BoujeeEnjinia1701/breakhook/cad/drawings/BHK-DWG-001.pdf

PRELIMINARY, NOT FOR FABRICATION | BreakHook · github.com/BoujeeEnjinia1701/breakhook

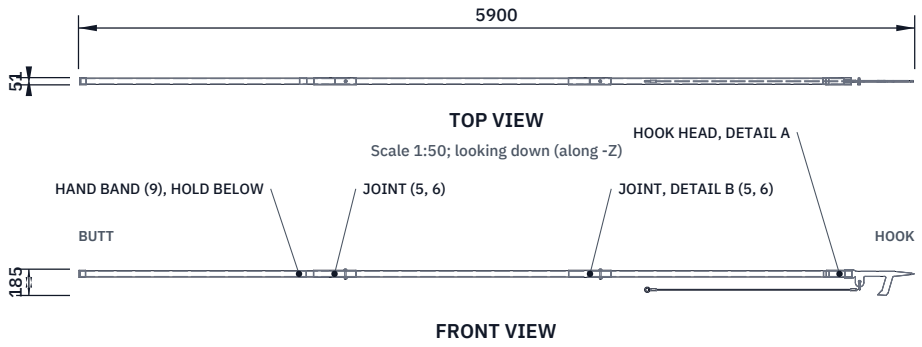
[picture p40: figure]
FRONT VIEW; TOP VIEW; Scale 1:50; looking down (along -Z); HAND BAND (9), HOLD BELOW; JOINT (5, 6); JOINT, DETAIL B (5, 6); HOOK HEAD, DETAIL A; BUTT; HOOK

Scale 1:50; looking at the front (along +Y)

RIGHT VIEW
Scale 1:50; looking at the right side (along -X)
1800 + CAP | 1800 | 1800 | HEAD

5900 OVERALL

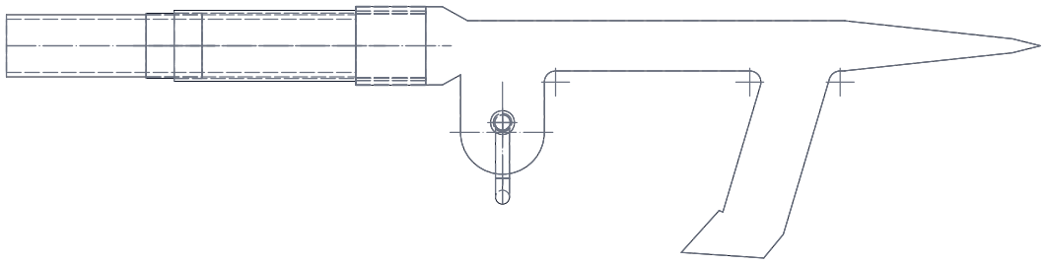
[picture p41: figure]

DETAIL A: HOOK HEAD
Scale 1:5; looking at the front (along +Y); pole tip shown cut short

DETAIL B: POLE JOINT
Scale 1:5; looking at the front (along +Y); sleeve bonded to the lower section

DETAIL C: FORK PROP (BOM 26 TO 31)
Scale 1:10; closed to 1.24 m, foot left, fork right; carried separately, sets the pole at mid-length

MAIN DIMENSIONS AND INTERFACES (MM)
Overall 5900; three sections 1800, 44.5 x 3.2 fibreglass, foam filled Joints: sleeve 50.8 x 3.2 x 300, bonded 150; nylon pin 10, 75 above joint Socket 50.8 x 2.0 x 180; pole goes in 130, 1.15 radial clearance
Plate 10 S355 in two 10.5 x 50 slots; four 6 fillet welds outside
Arm reaches 117 below the shank; throat 150 at the shank
Shackle hole 13, in line with the arm; 3/8 in bow shackle, WLL 1 t Leader 6 wire rope, 1500 eye to eye; pull rope 12 polyester, 25 m
Hand band 1550 from the butt; insulated length 3674
Pole and hook head 7.8 kg; working pull 3 kN, proof 6 kN
Fork prop 1.1 kg, notch 1.19 to 1.94 m; under the pole 2944 from the butt Third angle; pole along X, hook at +X; (n) = BOM line
REV | DESCRIPTION | DATE | BY
P1 | Preliminary GA of the constructable design (TRL 3; BHK-DDR-002) | 2026-10-03 | AC
P2 | Fork prop added, detail C (BHK-DDR-003) | 2026-10-03 | AC
BREAKHOOK | github.com/BoujeeEnjinia1701/breakhook

## Firebreak hook and pole set: general arrangement

DRAWING NO.
BHK-DWG-001

REV
P2

SHEET
1 of 1

SIZE

## ANSI B

SCALE
1:50

UNITS
mm
PROJECTION | DATE
2026-10-03

DRAWN
Amish Chadha

MATERIAL / NOTES
Hook head S355 plate in 50.8 x 2.0 steel tube, primed and painted; pole foam-filled fibreglass tube 44.5 x 3.2; see bom/bom.csv
Licensed CERN-OHL-S-2.0 · Design Molecule Lab · designmolecule.com | Generated from cad/src; do not edit by hand
