BoujeeEnjinia1701/breakhook/cad/drawings/BHK-DWG-101.pdf

### BUILD PLAN SKETCH, PLAN NOT YET BUILT BreakHook · github.com/BoujeeEnjinia1701/breakhook

FRONT VIEW
Scale 1:5; looking at the front (along +Y)

TOP VIEW
Scale 1:5; looking down (along -Z)

RIGHT VIEW
Scale 1:5; looking at the right side (along -X)

490

10 180

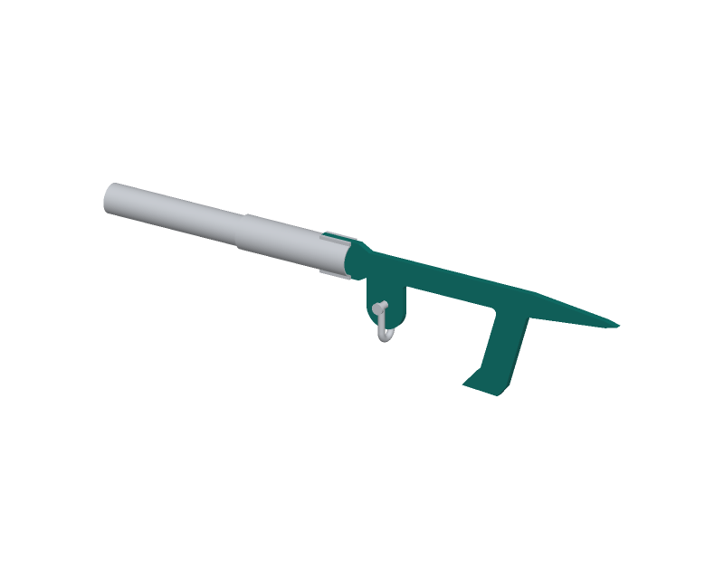
[picture p42: figure]

WHERE IT GOES
This part in colour, its neighbours in grey

HOW TO MAKE IT AND HOW IT FITS
Cut from 10 mm S355 plate, blank 500 x 200; one piece, no forging
Spike: tip on the centre line, 440 from the socket end of the plate
Shank 36 wide; the 56 wide end (62 long) goes into the socket slots
Arm 48 wide hangs 117 below the shank, raked back 17 deg; barb at its foot Rope tab under the shank, 25 to 85 from the socket end, round end R30 Shackle hole 13, centred 55 from the socket end and 55 below the axis Inside corners at the arm and tab: drill 16 and file to R8; no sharp notch Cut by plasma or chain drill and grinder; dress all edges, break corners 1 Throat between tab and arm: 150 wide at the shank, 128 at 100 below Fits: plate stands 2.6 proud of the tube top and bottom for the welds Check: lay on the full-size print; every edge within 1 mm
Stamp WLL 3 kN and the serial number on the shank before painting
REV | DESCRIPTION | DATE | BY
P1 | Making sketch for the prototype build plan | 2026-10-03 | AC
BREAKHOOK | github.com/BoujeeEnjinia1701/breakhook

## Hook plate: making sketch

DRAWING NO.
BHK-DWG-101

REV
P1

SHEET
1 of 1

SIZE

## ANSI B

SCALE
1:5

UNITS
mm
PROJECTION | DATE
2026-10-03

DRAWN
Amish Chadha

MATERIAL / NOTES
10 mm S355 steel plate, one per set
Licensed CERN-OHL-S-2.0 · Design Molecule Lab · designmolecule.com | Generated from cad/src; do not edit by hand
