BoujeeEnjinia1701/breakhook/cad/drawings/BHK-DWG-102.pdf

### BUILD PLAN SKETCH, PLAN NOT YET BUILT BreakHook · github.com/BoujeeEnjinia1701/breakhook

FRONT VIEW
Scale 1:2; looking at the front (along +Y)

TOP VIEW
Scale 1:2; looking down (along -Z)

RIGHT VIEW
Scale 1:2; looking at the right side (along -X)

180

51 51

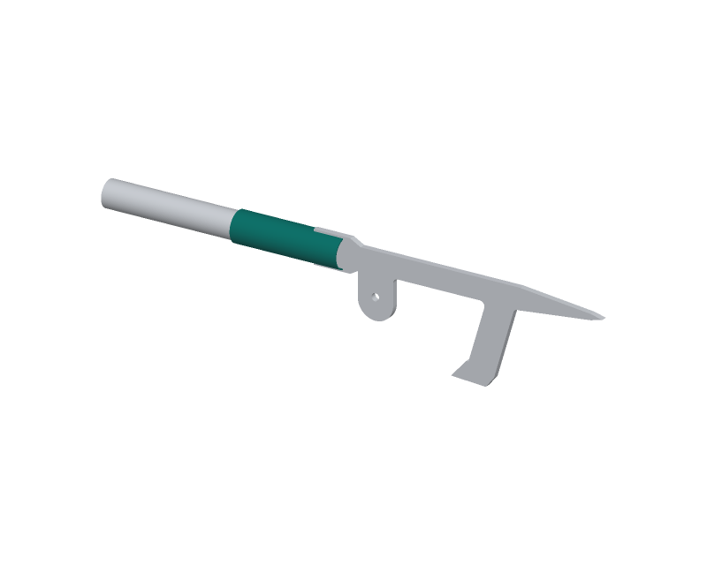
[picture p43: figure]

WHERE IT GOES
This part in colour, its neighbours in grey

HOW TO MAKE IT AND HOW IT FITS
Cut 180 long from 50.8 x 2.0 welded steel tube; square the ends
Slot one end across a diameter: two slots 10.5 wide, 50 deep, top and bottom Mark the slots with a strip of paper round the tube so they line up
Cut with a hacksaw or thin cutting disc; file to 10.5, square at the root
Deburr the bore at the open end and break its edge 1 x 45 deg
The bore is 46.8: the 44.5 pole slides in with 1.15 clearance each side The pole goes in 130 and stops against the end of the plate
Fits: the plate slides into both slots with no more than 0.5 total play Check: a 300 offcut of pole tube slides in and out by hand
REV | DESCRIPTION | DATE | BY
P1 | Making sketch for the prototype build plan | 2026-10-03 | AC
BREAKHOOK | github.com/BoujeeEnjinia1701/breakhook

## Socket tube: making sketch

DRAWING NO.
BHK-DWG-102

REV
P1

SHEET
1 of 1

SIZE

## ANSI B

SCALE
1:2

UNITS
mm
PROJECTION | DATE
2026-10-03

DRAWN
Amish Chadha

MATERIAL / NOTES
Welded steel tube 50.8 x 2.0, one per set
Licensed CERN-OHL-S-2.0 · Design Molecule Lab · designmolecule.com | Generated from cad/src; do not edit by hand
