BoujeeEnjinia1701/breakhook/cad/drawings/BHK-DWG-103.pdf

### BUILD PLAN SKETCH, PLAN NOT YET BUILT BreakHook · github.com/BoujeeEnjinia1701/breakhook

FRONT VIEW
Scale 1:10; looking at the front (along +Y)

TOP VIEW
Scale 1:10; looking down (along -Z)

RIGHT VIEW
Scale 1:10; looking at the right side (along -X)

1800

44 44

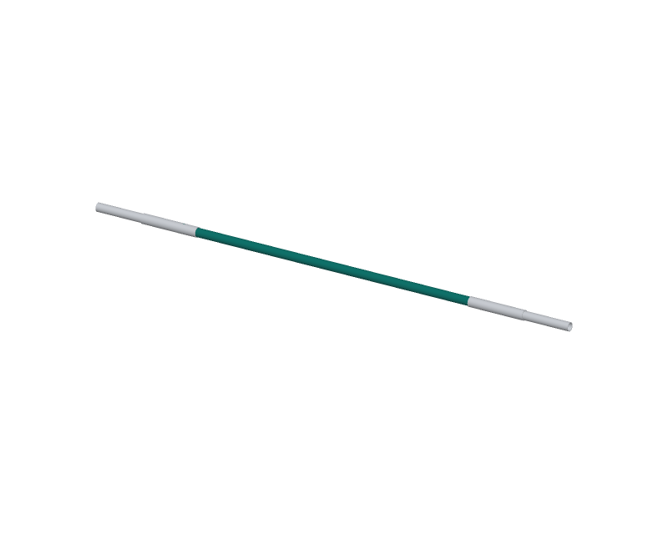
[picture p44: figure]

WHERE IT GOES
This part in colour, its neighbours in grey

HOW TO MAKE IT AND HOW IT FITS
Cut three lengths of 1800 from foam-filled fibreglass tube 44.5 x 3.2 Fine-tooth saw with the tube wrapped in tape; wear a dust mask outdoors Seal every cut end with a thin coat of epoxy so water cannot get into the foam Middle and top sections: drill one 10.5 hole across the tube, 74 from the bottom end (75 above the joint line), square to the tube, through both walls Butt section: no pin hole; its sleeve is bonded at its top end
Middle section: sleeve bonded at its top end; pin hole at its bottom end Top section: pin hole at its bottom end; friction ring at its top end
Coat each pin hole bore with epoxy as well
Check: each section 1800 within 2; holes square to the tube by eye
REV | DESCRIPTION | DATE | BY
P1 | Making sketch for the prototype build plan | 2026-10-03 | AC
BREAKHOOK | github.com/BoujeeEnjinia1701/breakhook

## Pole section (make 3): making sketch

DRAWING NO.
BHK-DWG-103

REV
P1

SHEET
1 of 1

SIZE

## ANSI B

SCALE
1:10

UNITS
mm
PROJECTION | DATE
2026-10-03

DRAWN
Amish Chadha

MATERIAL / NOTES
Foam-filled fibreglass tube 44.5 x 3.2, electrical grade
Licensed CERN-OHL-S-2.0 · Design Molecule Lab · designmolecule.com | Generated from cad/src; do not edit by hand
