BoujeeEnjinia1701/breakhook/cad/drawings/BHK-DWG-104.pdf

### BUILD PLAN SKETCH, PLAN NOT YET BUILT BreakHook · github.com/BoujeeEnjinia1701/breakhook

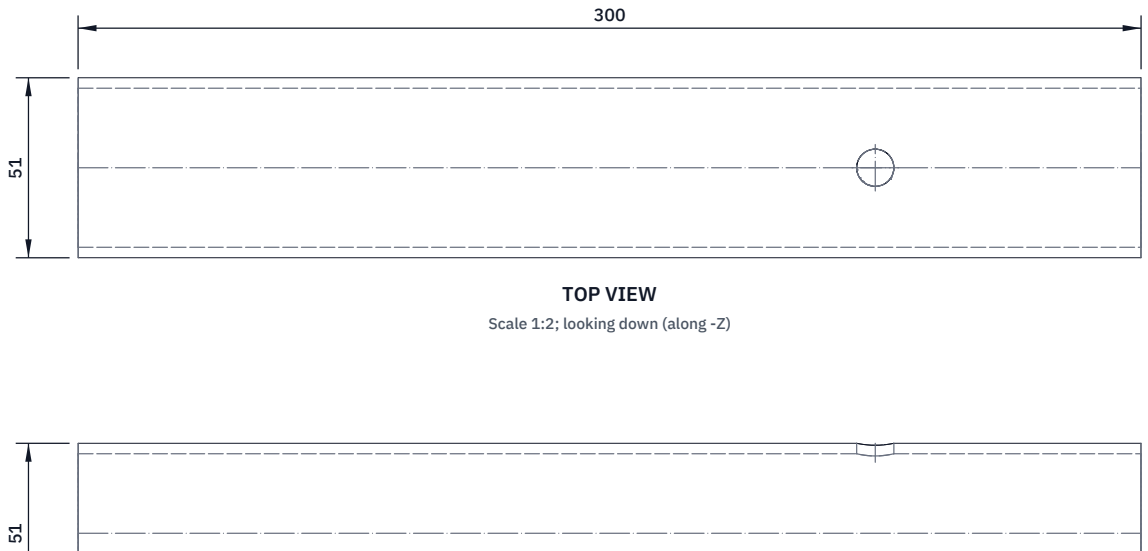
[picture p45: figure]
TOP VIEW; Scale 1:2; looking down (along -Z)

FRONT VIEW
Scale 1:2; looking at the front (along +Y)

RIGHT VIEW
Scale 1:2; looking at the right side (along -X)

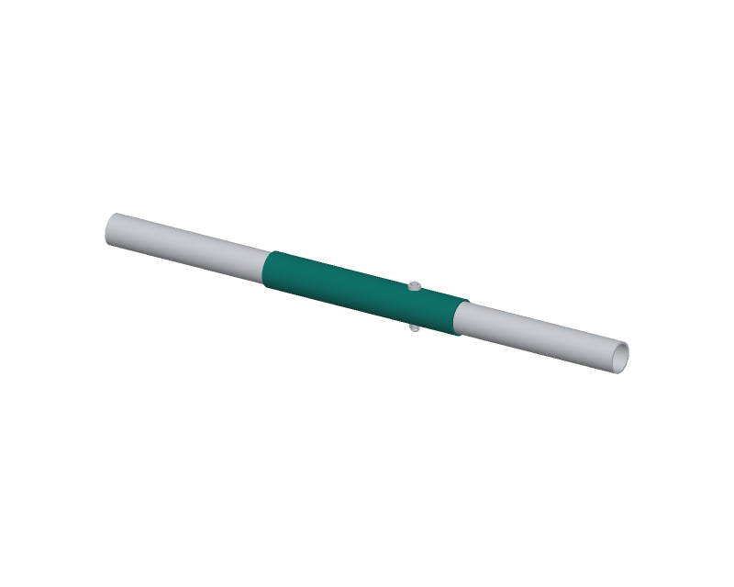
[picture p46: figure]

WHERE IT GOES
This part in colour, its neighbours in grey

HOW TO MAKE IT AND HOW IT FITS
Cut two lengths of 300 from 50.8 x 3.2 fibreglass tube; seal the ends
Sand the bore with coarse paper on a dowel until the pole tube slides in (about 0.2 clearance each side); try it often, do not overdo it
Drill one 10.5 hole across the sleeve, 75 from the middle (225 from one end) Bond the other half (150) onto the top of the lower section with epoxy,
the hole end sticking up; wipe off squeeze-out; cure a full day
Then slide the upper section in, drill through its pin hole into line
Check: upper section slides in and out by hand; the pin goes through both
REV | DESCRIPTION | DATE | BY
P1 | Making sketch for the prototype build plan | 2026-10-03 | AC
BREAKHOOK | github.com/BoujeeEnjinia1701/breakhook

## Joint sleeve (make 2): making sketch

DRAWING NO.
BHK-DWG-104

REV
P1

SHEET
1 of 1

SIZE

## ANSI B

SCALE
1:2

UNITS
mm
PROJECTION | DATE
2026-10-03

DRAWN
Amish Chadha

MATERIAL / NOTES
Fibreglass tube 50.8 x 3.2, 300 long
Licensed CERN-OHL-S-2.0 · Design Molecule Lab · designmolecule.com | Generated from cad/src; do not edit by hand
