BoujeeEnjinia1701/breakhook/cad/drawings/BHK-DWG-105.pdf

### BUILD PLAN SKETCH, PLAN NOT YET BUILT BreakHook · github.com/BoujeeEnjinia1701/breakhook

FRONT VIEW
Scale 1:5; looking at the front (along +Y)

TOP VIEW
Scale 1:5; looking down (along -Z)

RIGHT VIEW
Scale 1:5; looking at the right side (along -X)

32

300 32

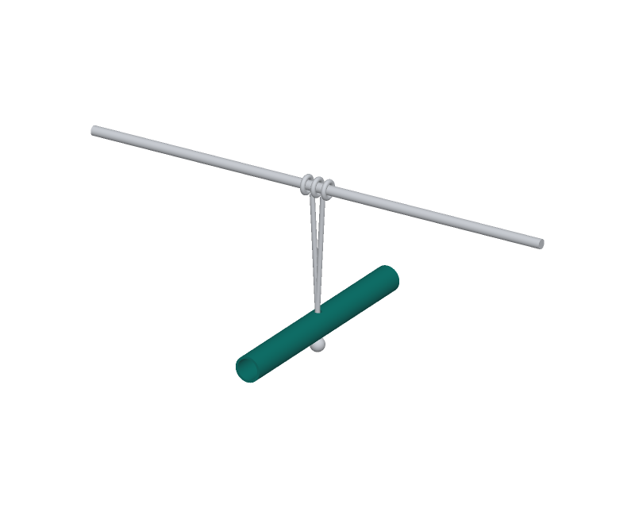
[picture p47: figure]

WHERE IT GOES
This part in colour, its neighbours in grey

HOW TO MAKE IT AND HOW IT FITS
Cut ten lengths of 300 from 32 x 3 fibreglass tube; round and seal the ends Drill a 10 hole straight across at mid length (150 from each end)
Sling: 1.2 m of 6 mm cord through the hole, tied into a loop with a
double fisherman's knot that sits under the toggle
Hitch the loop to the pull rope with a three-turn prusik hitch
(it slides when loose and grips when pulled)
Space the toggles 1 m apart, the first 11 m from the hook head Check: hang 30 kg on one toggle; the prusik must not slip
REV | DESCRIPTION | DATE | BY
P1 | Making sketch for the prototype build plan | 2026-10-03 | AC
BREAKHOOK | github.com/BoujeeEnjinia1701/breakhook

## Hauling toggle (make 10 per set): making sketch

DRAWING NO.
BHK-DWG-105

REV
P1

SHEET
1 of 1

SIZE

## ANSI B

SCALE
1:5

UNITS
mm
PROJECTION | DATE
2026-10-03

DRAWN
Amish Chadha

MATERIAL / NOTES
Fibreglass tube 32 x 3, 300 long
Licensed CERN-OHL-S-2.0 · Design Molecule Lab · designmolecule.com | Generated from cad/src; do not edit by hand
