BoujeeEnjinia1701/breakhook/cad/drawings/BHK-DWG-106.pdf

### BUILD PLAN SKETCH, PLAN NOT YET BUILT BreakHook · github.com/BoujeeEnjinia1701/breakhook

FRONT VIEW
Scale 1:10; looking at the front (along +Y)

TOP VIEW
Scale 1:10; looking down (along -Z)

RIGHT VIEW
Scale 1:10; looking at the right side (along -X)

40

386 800

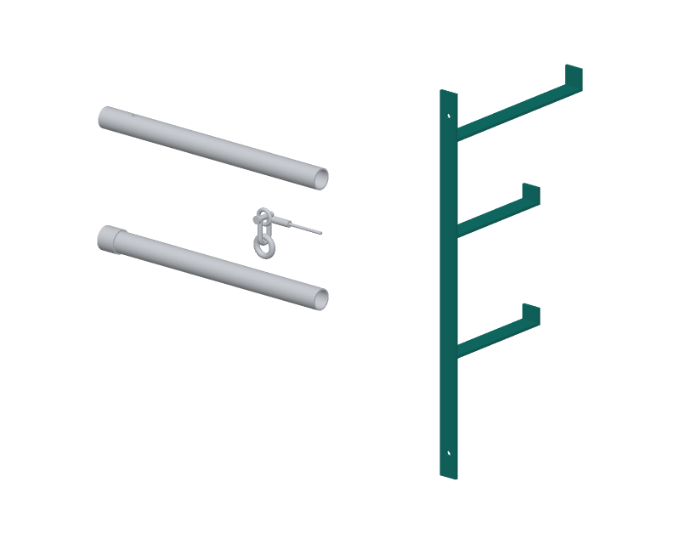
[picture p48: figure]

WHERE IT GOES
This part in colour, its neighbours in grey

HOW TO MAKE IT AND HOW IT FITS
Upright: 40 x 6 flat bar, 800 long; two 11 holes 50 and 750 up for M10 anchors Arms: two pieces 250 long, welded square to the front face, tops 256 and 506 up Lips: 30 tall, welded on the arm ends so poles cannot roll off
Rope peg: 380 long at 700 up with a 40 tall lip; the coil hangs clear
of the arms below it
Weld all round each arm root (5 fillet); grind smooth; prime and paint
Two uprights 1200 apart on a wall, out of the sun and rain where possible Each arm holds four poles 56 apart; sleeves go at alternate ends
Check: arms level and square to the wall; a 10 kg load leaves no movement
REV | DESCRIPTION | DATE | BY
P1 | Making sketch for the prototype build plan | 2026-10-03 | AC
BREAKHOOK | github.com/BoujeeEnjinia1701/breakhook

## Rack upright (make 2): making sketch

DRAWING NO.
BHK-DWG-106

REV
P1

SHEET
1 of 1

SIZE

## ANSI B

SCALE
1:10

UNITS
mm
PROJECTION | DATE
2026-10-03

DRAWN
Amish Chadha

MATERIAL / NOTES
40 x 6 steel flat bar, welded, primed and painted
Licensed CERN-OHL-S-2.0 · Design Molecule Lab · designmolecule.com | Generated from cad/src; do not edit by hand
