BoujeeEnjinia1701/breakhook/cad/drawings/BHK-DWG-107.pdf

### BUILD PLAN SKETCH, PLAN NOT YET BUILT BreakHook · github.com/BoujeeEnjinia1701/breakhook

FRONT VIEW
Scale 1:20; looking at the front (along +Y)

TOP VIEW
Scale 1:20; looking down (along -Z)

RIGHT VIEW
Scale 1:20; looking at the right side (along -X)

38

100 1991

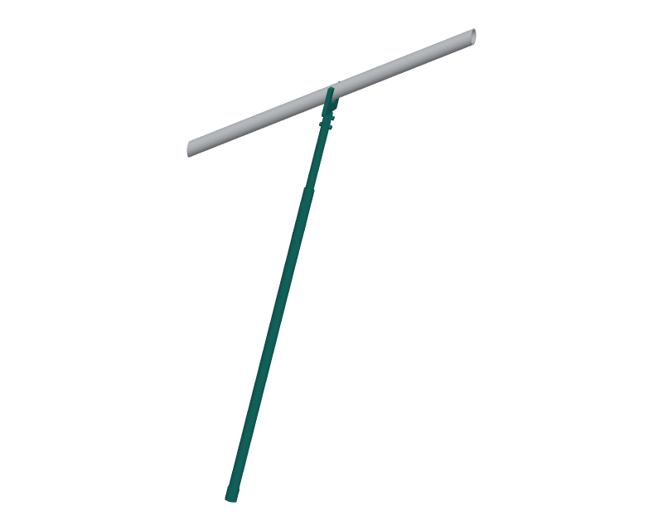
[picture p49: figure]

WHERE IT GOES
This part in colour, its neighbours in grey

HOW TO MAKE IT AND HOW IT FITS
Lower tube: 32 x 3 fibreglass, 1000 long; one 10.5 hole across, 50 below its top Upper tube: 25.4 x 3.2 fibreglass, 1100 long; it slides inside the lower tube (0.3 clearance each side); sixteen 10.5 holes, 50 apart, the first 150 up
from its bottom end; all holes in one line, square to the tube
Slot across the top of the upper tube: 12.5 wide, 60 deep (as the socket slots) Fork plate: 12 HDPE, 100 wide; notch 50 wide, round bottom R25, 30 above the tube top; tongue 25.4 wide, 60 long into the slot; round all edges
Two nylon M8 bolts through tube and tongue, 15 and 45 below the tube top Rubber foot cap; red band 850 to 900 up from the foot; hold below the band Notch height 1.19 to 1.94 m in 50 steps; 1.24 m long when closed
Seal cut ends and hole bores with epoxy; no metal anywhere in the prop Check: upper tube slides freely; the pin goes through at every hole
REV | DESCRIPTION | DATE | BY
P1 | Making sketch for the prototype build plan | 2026-10-03 | AC
BREAKHOOK | github.com/BoujeeEnjinia1701/breakhook

## Fork prop (make 1 per set): making sketch

DRAWING NO.
BHK-DWG-107

REV
P1

SHEET
1 of 1

SIZE

## ANSI B

SCALE
1:20

UNITS
mm
PROJECTION | DATE
2026-10-03

DRAWN
Amish Chadha

MATERIAL / NOTES
Fibreglass tube 32 x 3 and 25.4 x 3.2; 12 HDPE fork plate; nylon bolts and pin
Licensed CERN-OHL-S-2.0 · Design Molecule Lab · designmolecule.com | Generated from cad/src; do not edit by hand
