BoujeeEnjinia1701/breakhook/cad/drawings/BHK-DWG-001.png

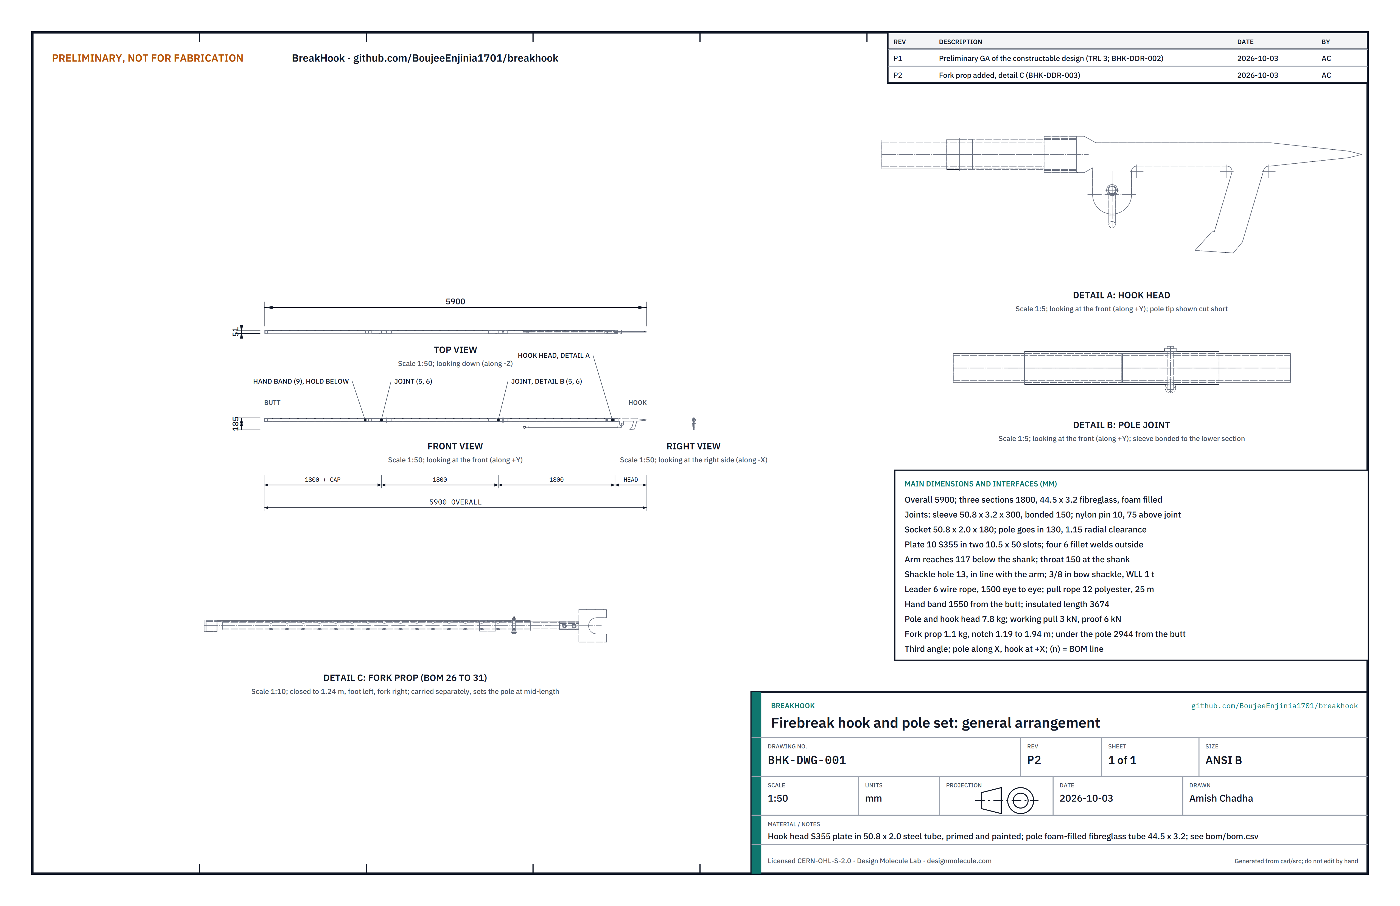
cad/drawings/BHK-DWG-001.png
