BoujeeEnjinia1701/breakhook/media/card.png

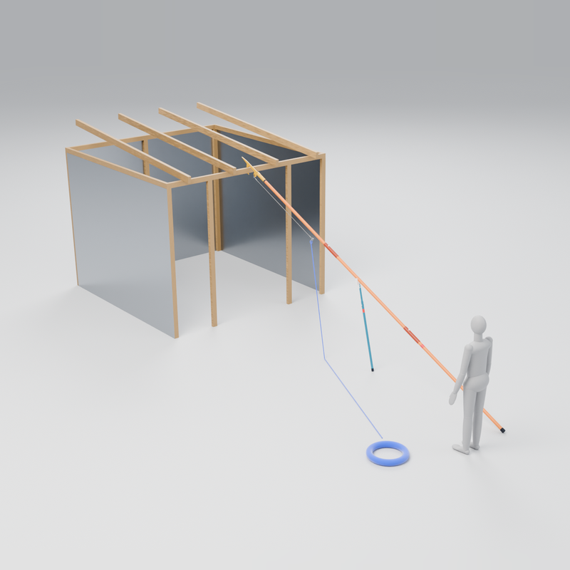
media/card.png
