BoujeeEnjinia1701/breakhook/media/render-detail.png

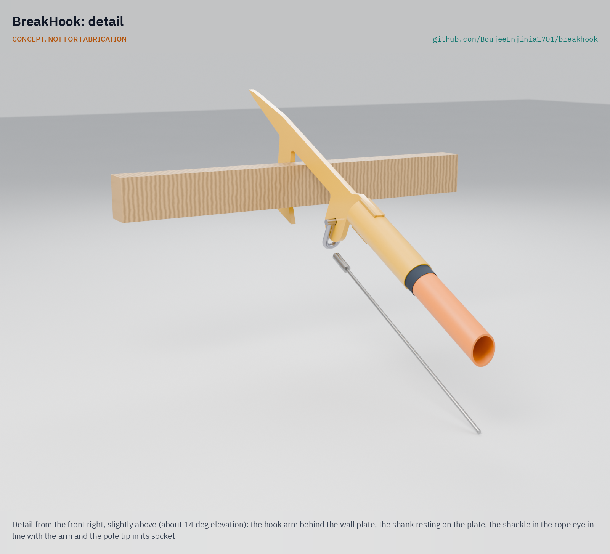
media/render-detail.png
