BoujeeEnjinia1701/breakhook/media/render-exploded.png

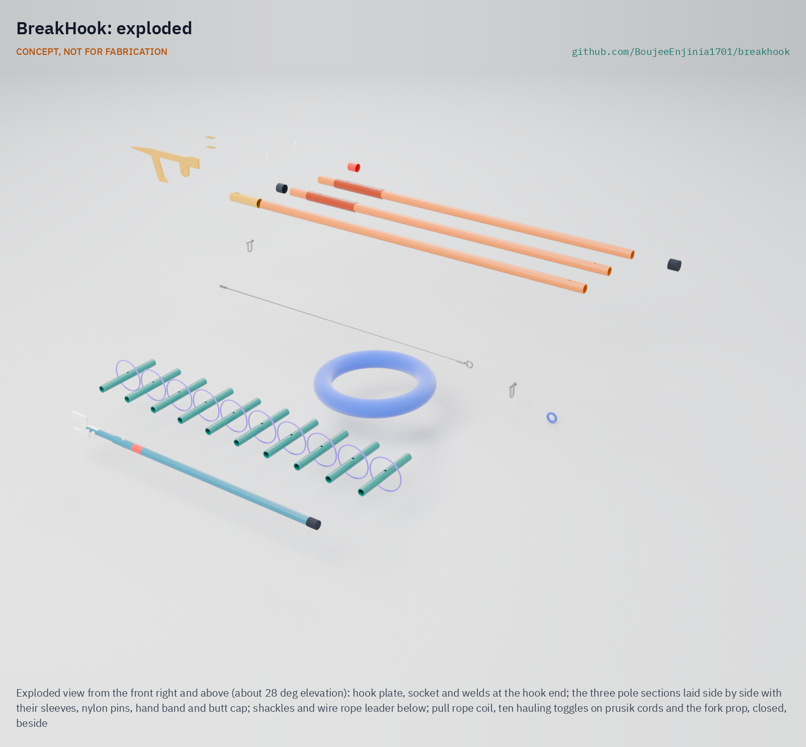
media/render-exploded.png
