BoujeeEnjinia1701/breakhook/media/social-preview.png

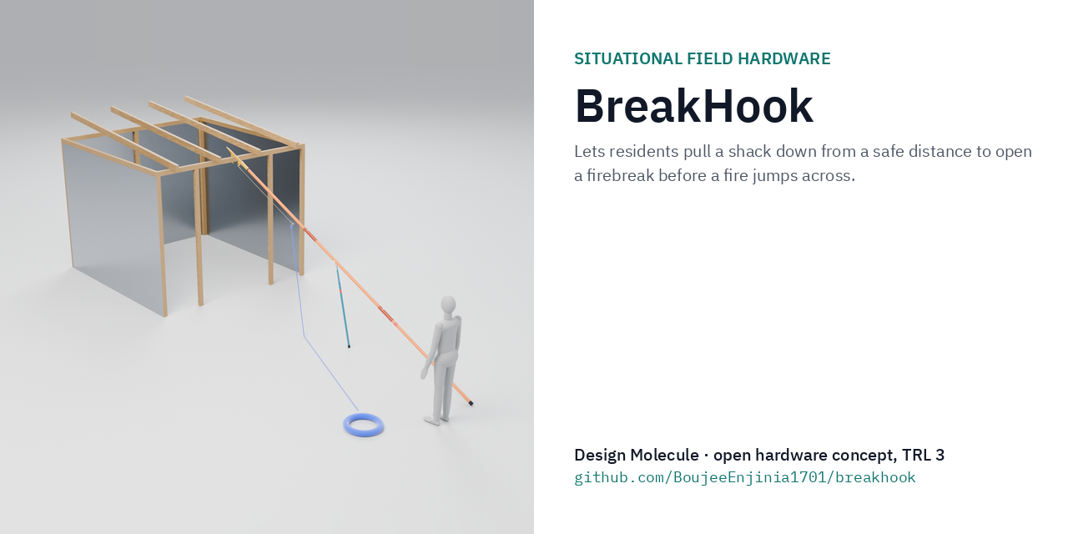
media/social-preview.png
